abhayap/SpHEAR/pictures/TinySpHEAR_10mm_alegs.png

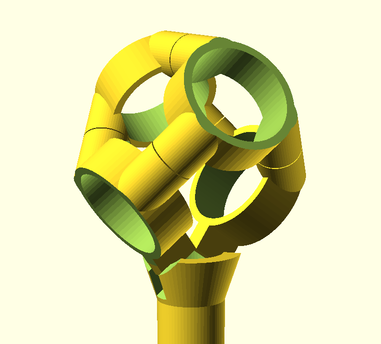
pictures/TinySpHEAR_10mm_alegs.png
