abhayap/SpHEAR/pictures/TinySpHEAR_prototype.png

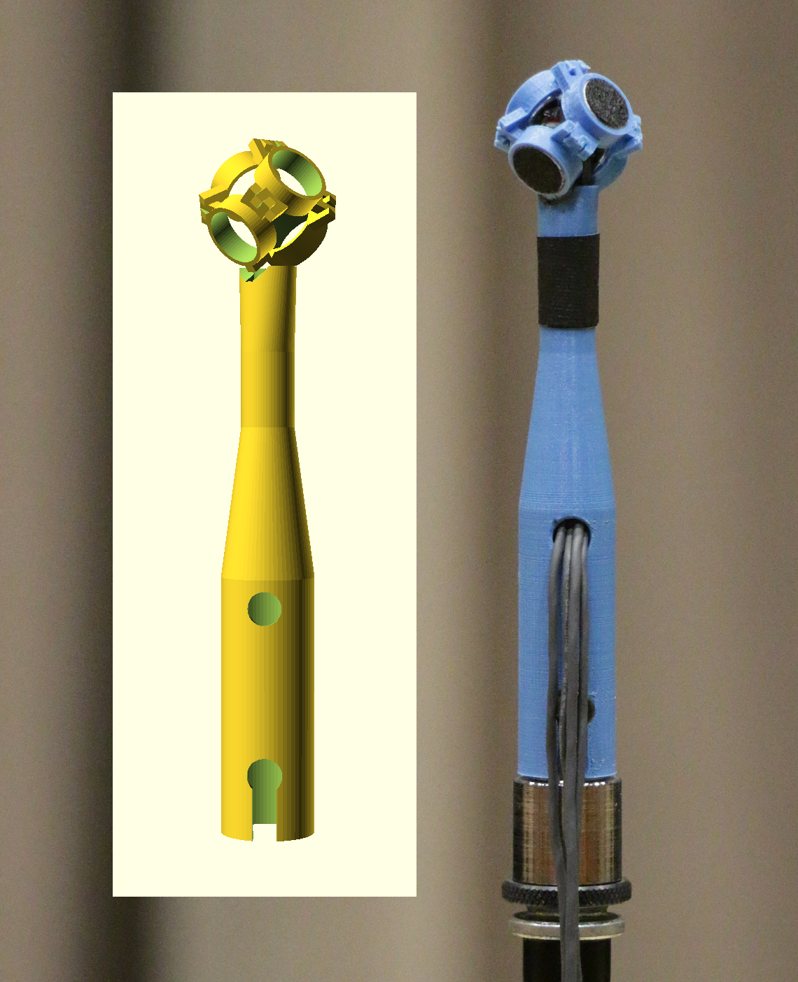
pictures/TinySpHEAR_prototype.png
