abhayap/SpHEAR/pictures/TinySpHEAR_zapnspark.png

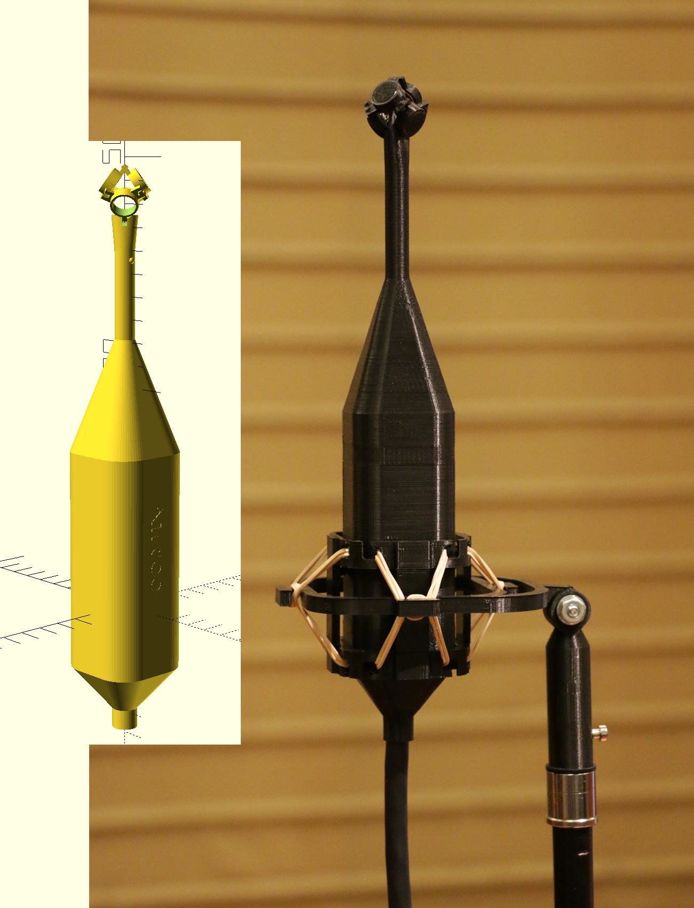
pictures/TinySpHEAR_zapnspark.png
