abhayap/SpHEAR/pictures/TinySpHEAR_zapnspark_3.png

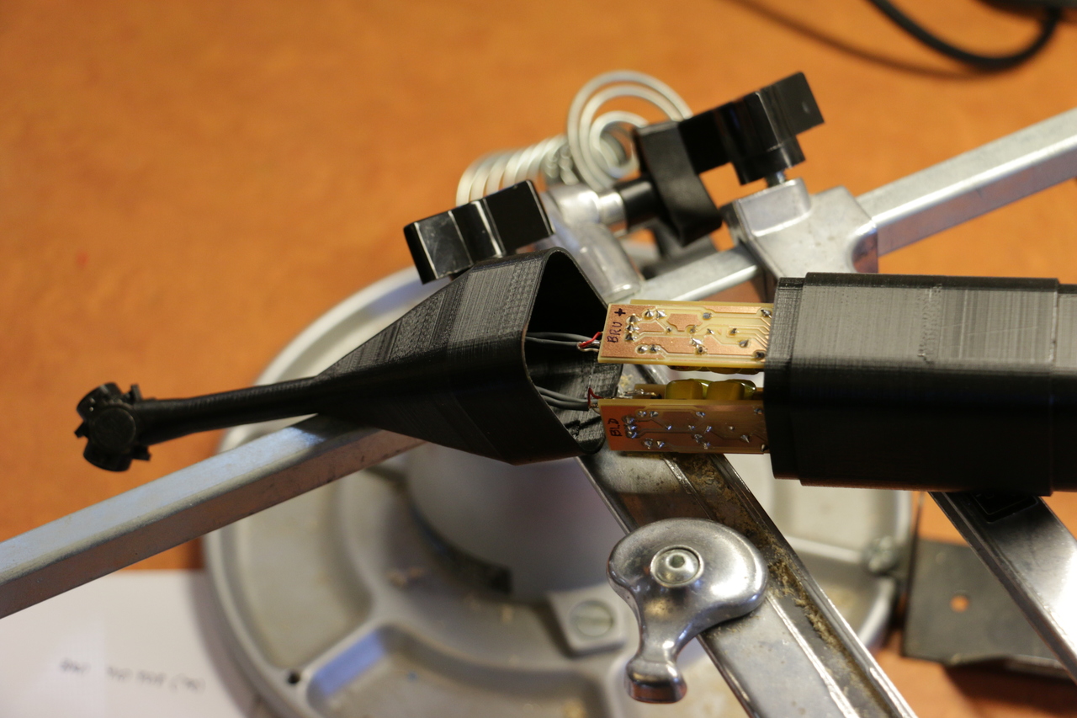
pictures/TinySpHEAR_zapnspark_3.png
