abhayap/SpHEAR/pictures/TinySpHEAR_zapnspark_4.png

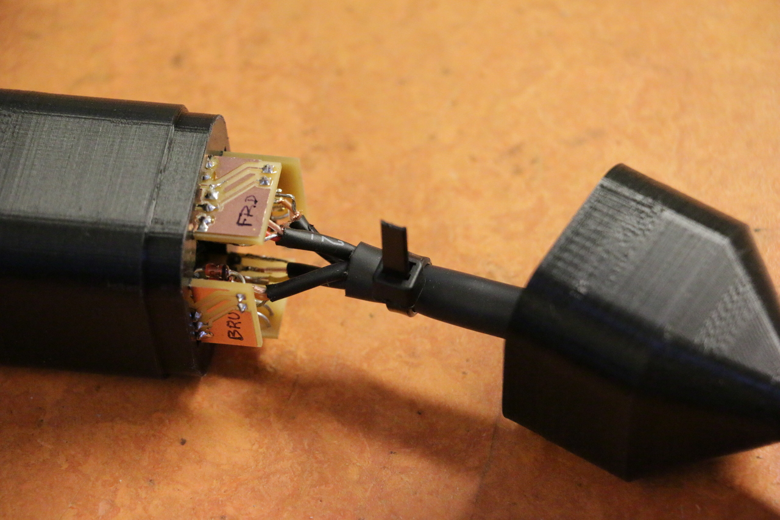
pictures/TinySpHEAR_zapnspark_4.png
