abhayap/SpHEAR/pictures/TinySpHEAR_zapnspark_5.png

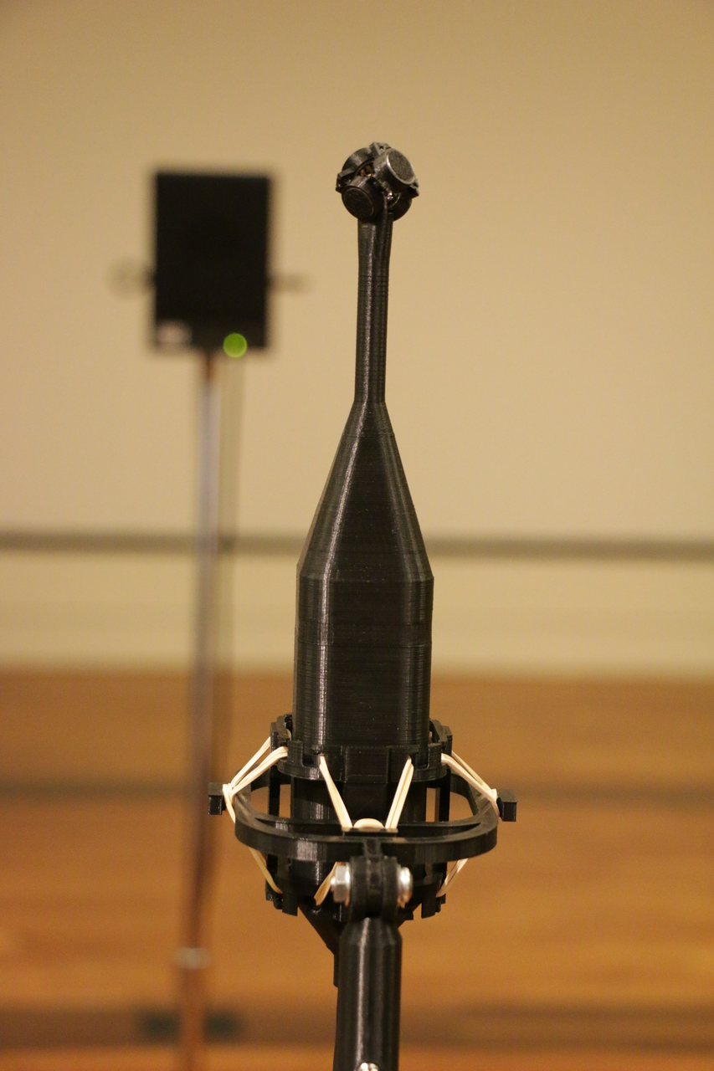
pictures/TinySpHEAR_zapnspark_5.png
