abhayap/SpHEAR/pictures/TinySpHEAR_zapnspark_6.png

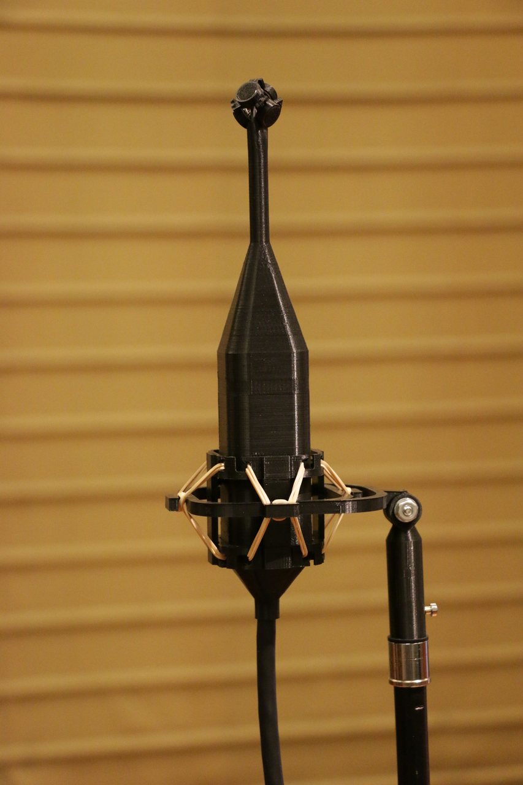
pictures/TinySpHEAR_zapnspark_6.png
