abhayap/SpHEAR/TestRig.scad

//
// Test Rig for Primo EM182 capsules
//
// Copyright 2015, Fernando Lopez-Lezcano, All Rights Reserved
// nando@ccrma.stanford.edu
//
//
//  This program is free software: you can redistribute it and/or modify
//  it under the terms of the GNU General Public License as published by
//  the Free Software Foundation, either version 3 of the License, or
//  (at your option) any later version.
//
//  This program is distributed in the hope that it will be useful,
//  but WITHOUT ANY WARRANTY; without even the implied warranty of
//  MERCHANTABILITY or FITNESS FOR A PARTICULAR PURPOSE.  See the
//  GNU General Public License for more details.
//
//  You should have received a copy of the GNU General Public License
//  along with this program.  If not, see <http://www.gnu.org/licenses/>.
//
//
// 3d Models released under the Creative Commons license as follows:
//   Attribution-NonCommercial-ShareAlike 4.0 International (CC BY-NC-SA 4.0)
// http://creativecommons.org/licenses/by-nc-sa/4.0/

// dimensions of the EM182 electret microphone
capsule_radius = 5;
capsule_radius_i = 2.2;
capsule_height = 4.5;

// wall thickness of capsule holder
wall = 1;

// contact pads
pad_offset = 3.56;

// slot for contact
// contact_width = 0.85;
contact_width = 1.00;

// length of contact
contact_length = 2.9;

// depth of contact channel (includes contact)
// contact_depth = 0.79;
contact_depth = 0.5;

// island around contact
contact_border = 0.5;

// contact offset from center line
contact_offset = 0.3;

// cutout offset from edge of capsule
contact_cutout = 2.0;
contact_cutout_gnd = 2.5;

// support depth
disk_depth = 0.9;
disk_edge = 0.49;
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
