abhayap/SpHEAR/pictures/TinySpHEAR_capsule_print.png

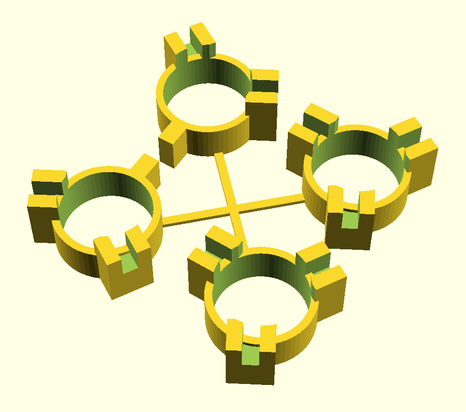
pictures/TinySpHEAR_capsule_print.png
